devonho/f408hs_control_board/spice/phase_sync.asc

C1: cap; 1µF
C2: cap; 10nF
D1: diode; 1N914
Q1: npn; 2N2222
R5: res; 1K
R25: res; 130K
R26: res; 130K
R27: res; 130K
R28: res; 18K
V1: voltage; SINE(0 240 50)
V2: voltage; 5
Named nets: 0
.tran 1s
