devonho/f408hs_control_board/spice/power.asc

0.68: cap; 0.82µ; V=200 Irms=5.01 Rser=0.0242154 Lser=0 mfg="KEMET" pn="C2220C824K2RAC" type="X7R"
C1: cap; 1µ; V=50 Irms=3.41 Rser=0.0133158 Lser=0 mfg="KEMET" pn="C1206C105K5RAC" type="X7R"
C2: cap; 1000µ
D1: diode; RRE02VS4S
D2: diode; RRE02VSM4S
D3: zener; 1N750
R1: res; 100
R2: res; 100
R3: res; 97
R4: res; 150
V1: voltage; SINE(0 220 50)
Named nets: 0, Vdd
.tran 200ms
